yanataka60/MZ80K_SD/JPEG/Rev1.5.5+MZ-80K Series(4).JPG

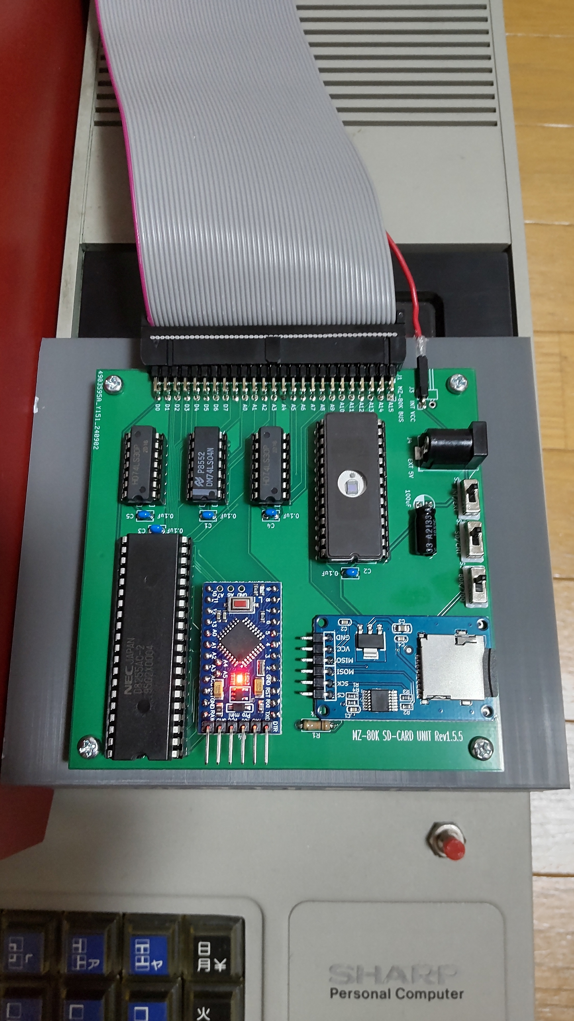
JPEG/Rev1.5.5+MZ-80K Series(4).JPG
