yanataka60/MZ80K_SD/JPEG/Rev1.5.5.JPG

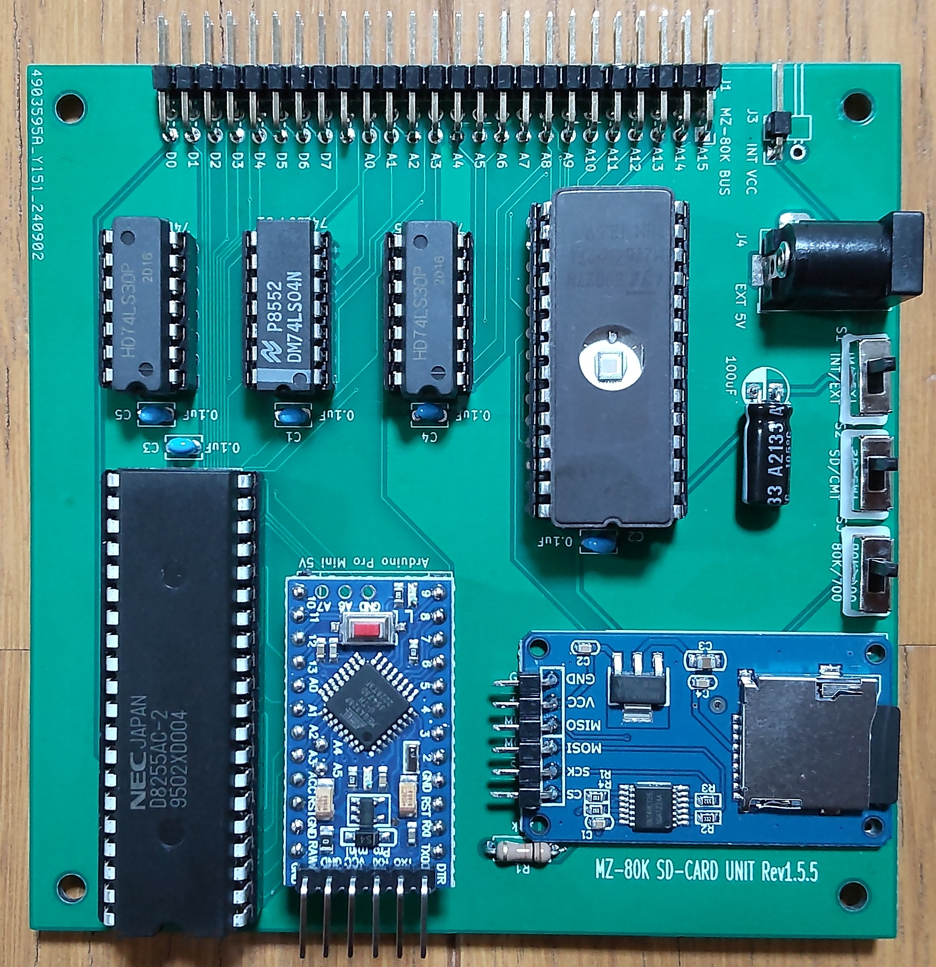
JPEG/Rev1.5.5.JPG
